earthtoernie/reciprocal_frequency_counter_earthtoernie/pico_display_oled/BitBang_I2C.c

//
// Bit Bang I2C library
// Copyright (c) 2018 BitBank Software, Inc.
// Written by Larry Bank (bitbank@pobox.com)
// Project started 10/12/2018
//
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
#include "pico/stdlib.h"
#include "hardware/gpio.h"
#include "pico/binary_info.h"
#include "hardware/i2c.h"

#include "BitBang_I2C.h"


//
// Transmit a byte and read the ack bit
// if we get a NACK (negative acknowledge) return 0
// otherwise return 1 for success
//
//
// Initialize the I2C BitBang library
// Pass the pin numbers used for SDA and SCL
// as well as the clock rate in Hz
//
void I2CInit(BBI2C *pI2C, uint32_t iClock)
{
    if (pI2C == NULL) return;
    if ((pI2C->iSDA + 2 * i2c_hw_index(pI2C->picoI2C))%4 != 0) return ;
    if ((pI2C->iSCL + 3 + 2 * i2c_hw_index(pI2C->picoI2C))%4 != 0) return ;
    i2c_init(pI2C->picoI2C, iClock);
    gpio_set_function(pI2C->iSDA, GPIO_FUNC_I2C);
    gpio_set_function(pI2C->iSCL, GPIO_FUNC_I2C);
    gpio_pull_up(pI2C->iSDA);
    gpio_pull_up(pI2C->iSCL);
    return;
}
//
// Test a specific I2C address to see if a device responds
// returns 0 for no response, 1 for a response
//
uint8_t I2CTest(BBI2C *pI2C, uint8_t addr)
{
    int ret;
    uint8_t rxdata;
    ret = i2c_read_blocking(pI2C->picoI2C, addr, &rxdata, 1, false);
    return (ret >= 0);
} /* I2CTest() */

//
// Scans for I2C devices on the bus
// returns a bitmap of devices which are present (128 bits = 16 bytes, LSB first)
// A set bit indicates that a device responded at that address
//
void I2CScan(BBI2C *pI2C, uint8_t *pMap)
{
    int i;
    for (i=0; i<16; i++) // clear the bitmap
        pMap[i] = 0;
    for (i=1; i<128; i++) // try every address
    {
        if (I2CTest(pI2C, i))
        {
            pMap[i >> 3] |= (1 << (i & 7));
        }
    }
} /* I2CScan() */


//
// Write I2C data
// quits if a NACK is received and returns 0
// otherwise returns the number of bytes written
//
int I2CWrite(BBI2C *pI2C, uint8_t iAddr, uint8_t *pData, int iLen)
{
    int rc = 0;

    rc = i2c_write_blocking(pI2C->picoI2C, iAddr, pData, iLen, true); // true to keep master control of bus
    return rc >= 0 ? iLen : 0;


} /* I2CWrite() */

//
// Read N bytes starting at a specific I2C internal register
//
int I2CReadRegister(BBI2C *pI2C, uint8_t iAddr, uint8_t u8Register, uint8_t *pData, int iLen)
{
    int rc;

    rc = i2c_write_blocking(pI2C->picoI2C, iAddr, &u8Register, 1, true); // true to keep master control of bus
    if (rc >= 0) {
        rc = i2c_read_blocking(pI2C->picoI2C, iAddr, pData, iLen, false);
    }
    return (rc >= 0);
} /* I2CReadRegister() */

//
// Read N bytes
//
int I2CRead(BBI2C *pI2C, uint8_t iAddr, uint8_t *pData, int iLen)
{
    int rc;
    rc = i2c_read_blocking(pI2C->picoI2C, iAddr, pData, iLen, false);
    return (rc >= 0);

} /* I2CRead() */

//
// Figure out what device is at that address
// returns the enumerated value
//
int I2CDiscoverDevice(BBI2C *pI2C, uint8_t i)
{
    uint8_t j, cTemp[8];
    int iDevice = DEVICE_UNKNOWN;

    if (i == 0x3c || i == 0x3d) // Probably an OLED display
    {
        I2CReadRegister(pI2C, i, 0x00, cTemp, 1);
        cTemp[0] &= 0xbf; // mask off power on/off bit
        if (cTemp[0] == 0x8) // SH1106
            iDevice = DEVICE_SH1106;
        else if (cTemp[0] == 3 || cTemp[0] == 6)
            iDevice = DEVICE_SSD1306;
        return iDevice;
    }

    if (i == 0x34 || i == 0x35) // Probably an AXP202/AXP192 PMU chip
    {
        I2CReadRegister(pI2C, i, 0x03, cTemp, 1); // chip ID
        if (cTemp[0] == 0x41)
            return DEVICE_AXP202;
        else if (cTemp[0] == 0x03)
            return DEVICE_AXP192;
    }

    if (i >= 0x40 && i <= 0x4f) // check for TI INA219 power measurement sensor
    {
        I2CReadRegister(pI2C, i, 0x00, cTemp, 2);
        if (cTemp[0] == 0x39 && cTemp[1] == 0x9f)
            return DEVICE_INA219;
    }

    // Check for Microchip 24AAXXXE64 family serial 2 Kbit EEPROM
    if (i >= 0x50 && i <= 0x57) {
        uint32_t u32Temp = 0;
        I2CReadRegister(pI2C, i, 0xf8, (uint8_t *)&u32Temp,
                        3); // check for Microchip's OUI
        if (u32Temp == 0x000004a3 || u32Temp == 0x00001ec0 ||
            u32Temp == 0x00d88039 || u32Temp == 0x005410ec)
            return DEVICE_24AAXXXE64;
    }

//  else if (i == 0x5b) // MLX90615?
//  {
//    I2CReadRegister(pI2C, i, 0x10, cTemp, 3);
//    for (j=0; j<3; j++) Serial.println(cTemp[j], HEX);
//  }
    // try to identify it from the known devices using register contents
    {
        // Check for TI HDC1080
        I2CReadRegister(pI2C, i, 0xff, cTemp, 2);
        if (cTemp[0] == 0x10 && cTemp[1] == 0x50)
            return DEVICE_HDC1080;

        // Check for BME680
        if (i == 0x76 || i == 0x77)
        {
            I2CReadRegister(pI2C, i, 0xd0, cTemp, 1); // chip ID
            if (cTemp[0] == 0x61) // BME680
                return DEVICE_BME680;
        }
        // Check for VL53L0X
        I2CReadRegister(pI2C, i, 0xc0, cTemp, 3);
        if (cTemp[0] == 0xee && cTemp[1] == 0xaa && cTemp[2] == 0x10)
            return DEVICE_VL53L0X;

        // Check for CCS811
        I2CReadRegister(pI2C, i, 0x20, cTemp, 1);
        if (cTemp[0] == 0x81) // Device ID
            return DEVICE_CCS811;

        // Check for LIS3DSH accelerometer from STMicro
        I2CReadRegister(pI2C, i, 0x0f, cTemp, 1);
        if (cTemp[0] == 0x3f) // WHO_AM_I
            return DEVICE_LIS3DSH;

        // Check for LIS3DH accelerometer from STMicro
        I2CReadRegister(pI2C, i, 0x0f, cTemp, 1);
        if (cTemp[0] == 0x33) // WHO_AM_I
            return DEVICE_LIS3DH;

        // Check for LSM9DS1 magnetometer/gyro/accel sensor from STMicro
        I2CReadRegister(pI2C, i, 0x0f, cTemp, 1);
        if (cTemp[0] == 0x68) // WHO_AM_I
            return DEVICE_LSM9DS1;

        // Check for LPS25H pressure sensor from STMicro
        I2CReadRegister(pI2C, i, 0x0f, cTemp, 1);
        if (cTemp[0] == 0xbd) // WHO_AM_I
            return DEVICE_LPS25H;

        // Check for HTS221 temp/humidity sensor from STMicro
        I2CReadRegister(pI2C, i, 0x0f, cTemp, 1);
        if (cTemp[0] == 0xbc) // WHO_AM_I
            return DEVICE_HTS221;

        // Check for MAG3110
        I2CReadRegister(pI2C, i, 0x07, cTemp, 1);
        if (cTemp[0] == 0xc4) // WHO_AM_I
            return DEVICE_MAG3110;

        // Check for LM8330 keyboard controller
        I2CReadRegister(pI2C, i, 0x80, cTemp, 2);
        if (cTemp[0] == 0x0 && cTemp[1] == 0x84) // manufacturer code + software revision
            return DEVICE_LM8330;

        // Check for MAX44009
        if (i == 0x4a || i == 0x4b)
        {
            for (j=0; j<8; j++)
                I2CReadRegister(pI2C, i, j, &cTemp[j], 1); // check for power-up reset state of registers
            if ((cTemp[2] == 3 || cTemp[2] == 2) && cTemp[6] == 0 && cTemp[7] == 0xff)
                return DEVICE_MAX44009;
        }

        // Check for ADS1115
        I2CReadRegister(pI2C, i, 0x02, cTemp, 2); // Lo_thresh defaults to 0x8000
        I2CReadRegister(pI2C, i, 0x03, &cTemp[2], 2); // Hi_thresh defaults to 0x7fff
        if (cTemp[0] == 0x80 && cTemp[1] == 0x00 && cTemp[2] == 0x7f && cTemp[3] == 0xff)
            return DEVICE_ADS1115;

        // Check for MCP9808
        I2CReadRegister(pI2C, i, 0x06, cTemp, 2); // manufacturer ID && get device ID/revision
        I2CReadRegister(pI2C, i, 0x07, &cTemp[2], 2); // need to read them individually
        if (cTemp[0] == 0 && cTemp[1] == 0x54 && cTemp[2] == 0x04 && cTemp[3] == 0x00)
            return DEVICE_MCP9808;

        // Check for BMP280/BME280
        I2CReadRegister(pI2C, i, 0xd0, cTemp, 1);
        if (cTemp[0] == 0x55) // BMP180
            return DEVICE_BMP180;
        else if (cTemp[0] == 0x58)
            return DEVICE_BMP280;
        else if (cTemp[0] == 0x60) // BME280
            return DEVICE_BME280;

        // Check for LSM6DS3
        I2CReadRegister(pI2C, i, 0x0f, cTemp, 1); // WHO_AM_I
        if (cTemp[0] == 0x69)
            return DEVICE_LSM6DS3;

        // Check for ADXL345
        I2CReadRegister(pI2C, i, 0x00, cTemp, 1); // DEVID
        if (cTemp[0] == 0xe5)
            return DEVICE_ADXL345;

        // Check for MPU-60x0i, MPU-688x, and MPU-9250
        I2CReadRegister(pI2C, i, 0x75, cTemp, 1);
        if (cTemp[0] == (i & 0xfe)) // Current I2C address (low bit set to 0)
            return DEVICE_MPU6000;
        else if (cTemp[0] == 0x71)
            return DEVICE_MPU9250;
        else if (cTemp[0] == 0x19)
            return DEVICE_MPU6886;

        // Check for DS3231 RTC
        I2CReadRegister(pI2C, i, 0x0e, cTemp, 1); // read the control register
        if (i == 0x68 &&
            cTemp[0] == 0x1c) // fixed I2C address and power on reset value
            return DEVICE_DS3231;

        // Check for DS1307 RTC
        I2CReadRegister(pI2C, i, 0x07, cTemp, 1); // read the control register
        if (i == 0x68 &&
            cTemp[0] == 0x03) // fixed I2C address and power on reset value
            return DEVICE_DS1307;

    }
    return iDevice;
} /* I2CDiscoverDevice() */
